jinagyue/ThermalEyes/firmware/Core/Inc/common.h

/*
 * common.h
 *
 *  Created on: Aug 11, 2023
 *      Author: colourfate
 */

#ifndef INC_COMMON_H_
#define INC_COMMON_H_

#include "usb_data_transfer.h"

#define count_of(a) (sizeof(a) / sizeof(a[0]))

#endif /* INC_COMMON_H_ */
