jinagyue/ThermalEyes/software/app/src/main/java/com/example/thermaleyes/ThermalDevice.java

package com.example.thermaleyes;

import android.hardware.usb.UsbDevice;
import android.hardware.usb.UsbDeviceConnection;
import android.hardware.usb.UsbManager;
import android.os.Build;
import android.util.Log;

import androidx.annotation.RequiresApi;

import com.felhr.usbserial.UsbSerialDevice;
import com.felhr.usbserial.UsbSerialInterface;

import java.io.IOException;
import java.nio.ByteBuffer;
import java.nio.charset.StandardCharsets;
import java.util.Arrays;
import java.util.HashMap;

public abstract class ThermalDevice {
    public final static int IMAGE_WIDTH = 32;
    public final static int IMAGE_HEIGHT = 24;
    public final static int FPS_8 = 8;
    public final static int FPS_4 = 4;

    private final static String TAG = ThermalDevice.class.getSimpleName();
    private final static int VENDOR_ID = 1155;
    private final static int PRODUCT_ID = 22336;
    private final static int IMAGE_PIXEL = IMAGE_WIDTH * IMAGE_HEIGHT;
    private final static int DATA_LEN = IMAGE_PIXEL * 2 + 2;

    private final static float MAX_RANGE = 20.0f;
    private UsbManager myUsbManager;
    private UsbSerialDevice mSerial;
    private int mFPS = FPS_8;

    @RequiresApi(api = Build.VERSION_CODES.O)
    private final UsbSerialInterface.UsbReadCallback mCallback =
            arg0 -> {
                try {
                    ThermalDataPacket packet = ThermalDataPacket.create(arg0);
                    if (packet == null) {
                        return;
                    }
                    if (packet.isInvalid()) {
                        return;
                    }

                    if (packet.getType() == ThermalDataPacket.TYPE_LOG) {
                        Log.i("ThermalBridge", new String(packet.getData(), StandardCharsets.UTF_8));
                        return;
                    }

                    if (packet.getType() != ThermalDataPacket.TYPE_DATA) {
                        return;
                    }

                    float[] tempData = getTemperatureData(packet.getData());
                    if (tempData == null || tempData.length < IMAGE_PIXEL) {
                        return;
                    }

                    float maxTemp = tempData[0];
                    float minTemp = tempData[0];
                    int maxLoc = 0;
                    int minLoc = 0;
                    for (int i = 0; i < tempData.length; i++) {
                        if (maxTemp < tempData[i]) {
                            maxTemp = tempData[i];
                            maxLoc = i;
                        }
                        if (minTemp > tempData[i]) {
                            minTemp = tempData[i];
                            minLoc = i;
                        }
                    }
                    int c1 = 11 * IMAGE_WIDTH + 15;
                    int c2 = 11 * IMAGE_WIDTH + 16;
                    int c3 = 12 * IMAGE_WIDTH + 15;
                    int c4 = 12 * IMAGE_WIDTH + 16;
                    float centerTemp = (tempData[c1] + tempData[c2] + tempData[c3] + tempData[c4]) / 4.0f;

                    ByteBuffer tempImage = getTemperatureImage(tempData, maxTemp, minTemp);
                    onFrame(tempImage, maxTemp, minTemp, centerTemp, maxLoc, minLoc);
                } catch (Throwable t) {
                    Log.e(TAG, "Thermal data parsing error: " + t.getMessage());
                }
            };

    public abstract void onFrame(ByteBuffer frame, float maxTemp, float minTemp, float centerTemp, int maxLoc, int minLoc);

    public void setUsbManager(UsbManager usbManager) {
        myUsbManager = usbManager;
    }

    public synchronized boolean isConnected() {
        return mSerial != null && mSerial.isOpen();
    }

    @RequiresApi(api = Build.VERSION_CODES.O)
    public synchronized void connect() throws IOException {
        if (mSerial != null && mSerial.isOpen()) {
            Log.i(TAG, "ThermalDevice already connected, skipping redundant connect");
            return;
        }
        disconnect();

        UsbDevice device = enumerateDevice(VENDOR_ID, PRODUCT_ID);
        if (device == null) {
            throw new IOException("Not find device");
        }

        UsbDeviceConnection deviceConnection = openDevice(device);
        if (deviceConnection == null) {
            throw new IOException("Connect device failed");
        }

        mSerial = UsbSerialDevice.createUsbSerialDevice(device, deviceConnection);
        if (mSerial == null) {
            Log.e(TAG, "createUsbSerialDevice failed");
            throw new IOException("Not support terminal");
        }

        Log.i(TAG, "Create CDC devices success");
        // No physical serial port, no need to set parameters
        mSerial.open();
        mSerial.read(mCallback);
    }

    public synchronized void disconnect() {
        if (mSerial != null) {
            try {
                mSerial.close();
            } catch (Exception e) {
                Log.e(TAG, "disconnect error: " + e.getMessage());
            }
            mSerial = null;
        }
    }

    public void setFPS(int fps) {
        if (fps != FPS_4 && fps != FPS_8) {
            return;
        }

        ThermalDataPacket packet = ThermalDataPacket.allocate(7);
        if (packet == null) {
            return;
        }

        // { 0, 0x80, 0, 0, 0x1, 0, fps }
        packet.setHeader();
        packet.setType(ThermalDataPacket.TYPE_CMD_FPS);
        packet.setLength();
        packet.setData(new byte[]{ (byte) fps });
        mSerial.write(packet.array());
        mFPS = fps;
    }

    public int getFPS() {
        return mFPS;
    }

    private UsbDevice enumerateDevice(int vendorId, int productId) {
        if (myUsbManager == null) {
            Log.e(TAG, "Class not instantiate");
            return null;
        }

        HashMap<String, UsbDevice> deviceList = myUsbManager.getDeviceList();
        if (deviceList.isEmpty()) {
            Log.e(TAG, "Not usb device connect");
            return null;
        }

        for (UsbDevice device : deviceList.values()) {
            Log.i(TAG, "DeviceInfo: " + device.getVendorId() + " , "
                    + device.getProductId());

            if (device.getVendorId() == vendorId && device.getProductId() == productId) {
                Log.i(TAG, "enumerate device success");
                return device;
            }
        }

        return null;
    }

    private UsbDeviceConnection openDevice(UsbDevice device) {
        // specified by AndroidManifest.xml and res/xml/device_filter.xml
        if (myUsbManager.hasPermission(device)) {
            return myUsbManager.openDevice(device);
        } else {
            Log.e(TAG, "openDevice: Not permission vid: " + device.getVendorId());
            return null;
        }
    }

    @RequiresApi(api = Build.VERSION_CODES.O)
    private float[] getTemperatureData(byte[] thermalData) {
        float[] tempData = new float[IMAGE_PIXEL];

        Log.i(TAG, "data length: " + thermalData.length);
        for (int i = 0; i < tempData.length; i++) {
            int lowByte = Byte.toUnsignedInt(thermalData[2 * i]);
            int highByte = Byte.toUnsignedInt(thermalData[2 * i + 1]);

            tempData[i] = ((short)(highByte << 8 | lowByte)) / 100.0f;
        }

        return tempData;
    }

    private ByteBuffer getTemperatureImage(float[] tempMatrix, float maxTemp, float minTemp) {
        /* Only luminance */
        ByteBuffer buffer = ByteBuffer.allocate(tempMatrix.length);
        float range = Math.max(maxTemp - minTemp, MAX_RANGE);

        for (float tmp : tempMatrix) {
            int gray = (int) ((tmp - minTemp) / range * 255);
            buffer.put((byte) gray);
        }

        buffer.position(0);
        return buffer;
    }

    private static class ThermalDataPacket {
        public static final int TYPE_CMD_FPS = 0;
        public static final int TYPE_DATA = 1;
        public static final int TYPE_LOG = 2;
        private static final int MAX_SIZE = 2048;
        private final byte[] mData;

        ThermalDataPacket(byte[] data) {
            mData = data;
        }

        public static ThermalDataPacket create(byte[] data) {
            if (data.length <= 6) {
                return null;
            }

            return new ThermalDataPacket(data);
        }

        public static ThermalDataPacket allocate(int length) {
            if (length > MAX_SIZE) {
                return null;
            }
            return new ThermalDataPacket(new byte[length]);
        }

        public boolean isInvalid() {
            return getHeader() != 0x8000 || getLength() == 0 || (getLength() + 6 != mData.length);
        }

        public void setHeader() {
            mData[0] = 0;
            mData[1] = (byte) 0x80;
        }

        public int getHeader() {
            return Byte.toUnsignedInt(mData[0]) | Byte.toUnsignedInt(mData[1]) << 8;
        }

        public void setType(int type) {
            mData[2] = (byte) type;
            mData[3] = (byte) (type >> 8);
        }

        public int getType() {
            return Byte.toUnsignedInt(mData[2]) | Byte.toUnsignedInt(mData[3]) << 8;
        }

        public void setLength() {
            int len = mData.length - 6;

            if (len < 0) {
                len = 0;
            }
            mData[4] = (byte) len;
            mData[5] = (byte) (len >> 8);
        }

        public int getLength() {
            return Byte.toUnsignedInt(mData[4]) | Byte.toUnsignedInt(mData[5]) << 8;
        }

        public void setData(byte[] data) {
            System.arraycopy(data, 0, mData, 6, data.length);
        }

        public byte[] getData() {
            return Arrays.copyOfRange(mData, 6, 6 + getLength());
        }

        public byte[] array() {
            return mData;
        }
    }
}
